nimitvijayvargee/zenithkb/pcb/zenithkb/led.kicad_sch

## KiCad design pcb/zenithkb/led.kicad_sch (2026-05-24)

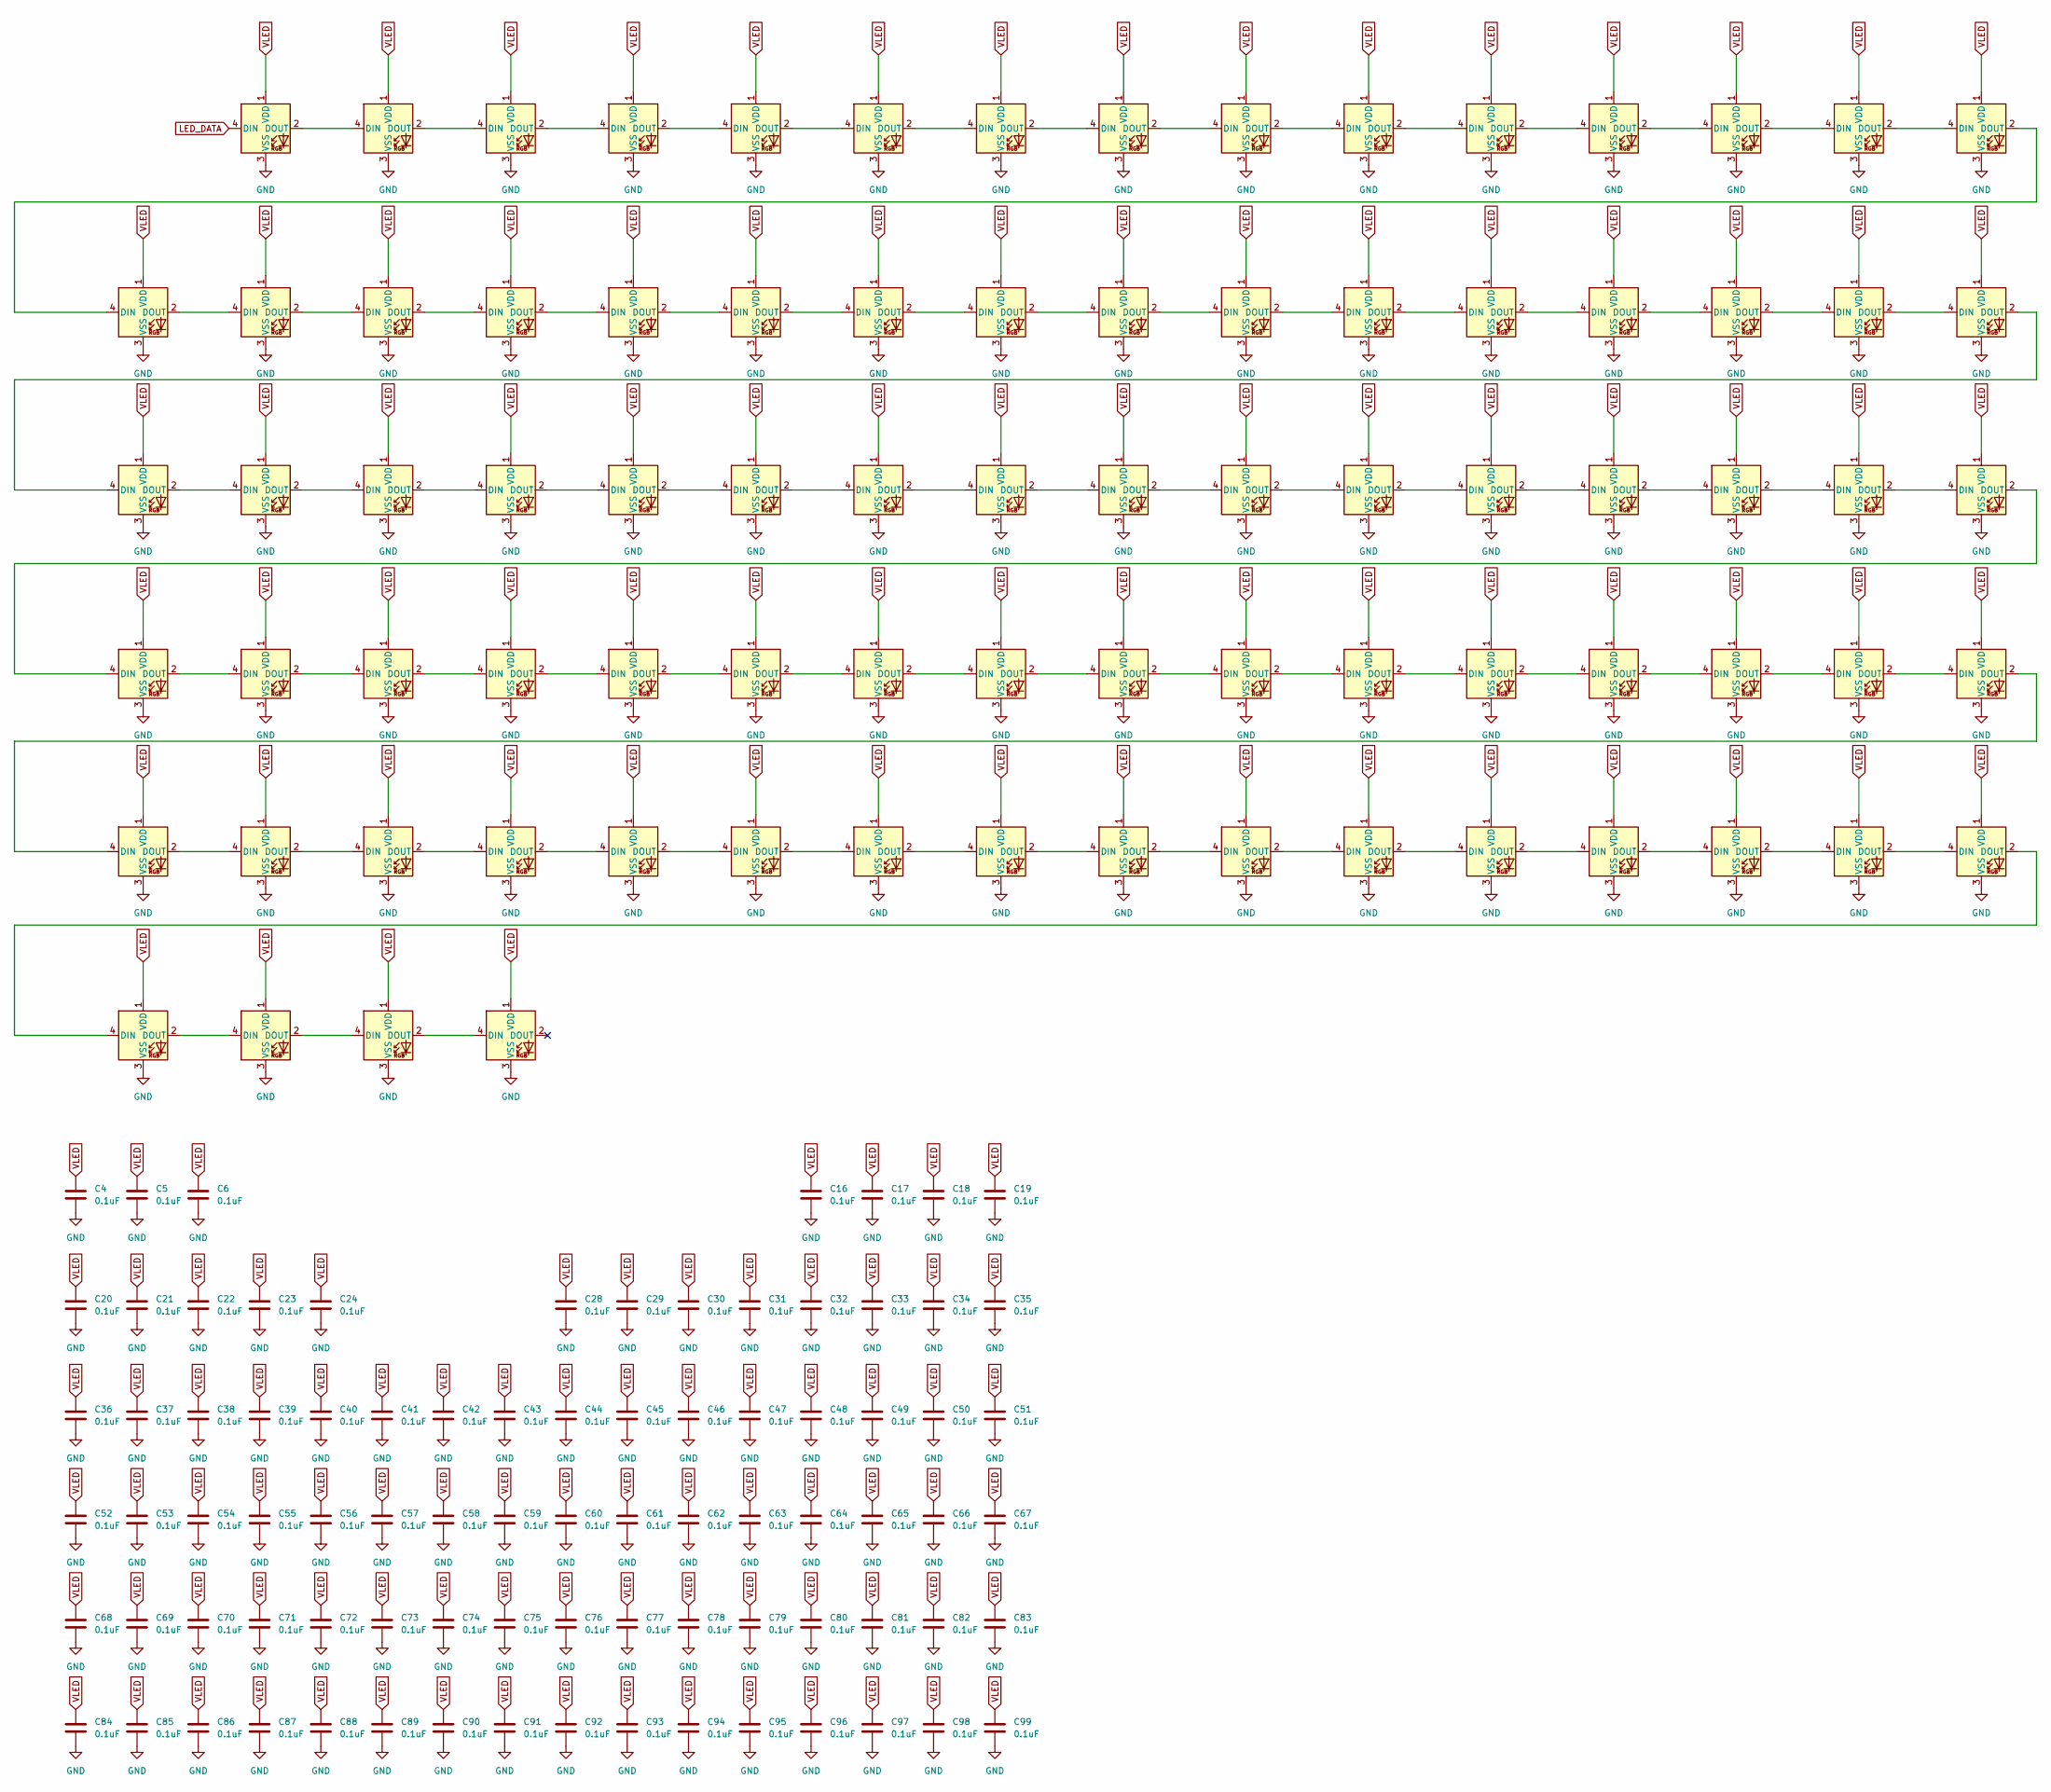
[picture p14: schematic led.kicad_sch]

Parts:
C4, C5, C6, C16, C17, C18, C19, C20, C21, C22, C23, C24, C28, C29, C30, C31, C32, C33, C34, C35, C36, C37, C38, C39, C40, C41, C42, C43, C44, C45, C46, C47, C48, C49, C50, C51, C52, C53, C54, C55, C56, C57, C58, C59, C60, C61, C62, C63, C64, C65, C66, C67, C68, C69, C70, C71, C72, C73, C74, C75, C76, C77, C78, C79, C80, C81, C82, C83, C84, C85, C86, C87, C88, C89, C90, C91, C92, C93, C94, C95, C96, C97, C98, C99: 0.1uF; C_Disc_D5.0mm_W2.5mm_P2.50mm
D86, D87, D88, D89, D90, D91, D92, D93, D94, D95, D96, D97, D98, D99, D100, D101, D102, D103, D104, D105, D106, D107, D108, D109, D110, D111, D112, D113, D114, D115, D116, D117, D118, D119, D120, D121, D122, D123, D124, D125, D126, D127, D128, D129, D130, D131, D132, D133, D134, D135, D136, D137, D138, D139, D140, D141, D142, D143, D144, D145, D146, D147, D148, D149, D150, D151, D152, D153, D154, D155, D156, D157, D158, D159, D160, D161, D162, D163, D164, D165, D166, D167, D168: LED_SK6812MINI; LCSC C5149201

Connections:
GND: C4.2, C5.2, C6.2, C16.2, C17.2, C18.2, C19.2, C20.2, C21.2, C22.2, C23.2, C24.2, C28.2, C29.2, C30.2, C31.2, C32.2, C33.2, C34.2, C35.2, C36.2, C37.2, C38.2, C39.2, C40.2, C41.2, C42.2, C43.2, C44.2, C45.2, C46.2, C47.2, C48.2, C49.2, C50.2, C51.2, C52.2, C53.2, C54.2, C55.2, C56.2, C57.2, C58.2, C59.2, C60.2, C61.2, C62.2, C63.2, C64.2, C65.2, C66.2, C67.2, C68.2, C69.2, C70.2, C71.2, C72.2, C73.2, C74.2, C75.2, C76.2, C77.2, C78.2, C79.2, C80.2, C81.2, C82.2, C83.2, C84.2, C85.2, C86.2, C87.2, C88.2, C89.2, C90.2, C91.2, C92.2, C93.2, C94.2, C95.2, C96.2, C97.2, C98.2, C99.2, D86.3 (VSS), D87.3 (VSS), D88.3 (VSS), D89.3 (VSS), D90.3 (VSS), D91.3 (VSS), D92.3 (VSS), D93.3 (VSS), D94.3 (VSS), D95.3 (VSS), D96.3 (VSS), D97.3 (VSS), D98.3 (VSS), D99.3 (VSS), D100.3 (VSS), D101.3 (VSS), D102.3 (VSS), D103.3 (VSS), D104.3 (VSS), D105.3 (VSS), D106.3 (VSS), D107.3 (VSS), D108.3 (VSS), D109.3 (VSS), D110.3 (VSS), D111.3 (VSS), D112.3 (VSS), D113.3 (VSS), D114.3 (VSS), D115.3 (VSS), D116.3 (VSS), D117.3 (VSS), D118.3 (VSS), D119.3 (VSS), D120.3 (VSS), D121.3 (VSS), D122.3 (VSS), D123.3 (VSS), D124.3 (VSS), D125.3 (VSS), D126.3 (VSS), D127.3 (VSS), D128.3 (VSS), D129.3 (VSS), D130.3 (VSS), D131.3 (VSS), D132.3 (VSS), D133.3 (VSS), D134.3 (VSS), D135.3 (VSS), D136.3 (VSS), D137.3 (VSS), D138.3 (VSS), D139.3 (VSS), D140.3 (VSS), D141.3 (VSS), D142.3 (VSS), D143.3 (VSS), D144.3 (VSS), D145.3 (VSS), D146.3 (VSS), D147.3 (VSS), D148.3 (VSS), D149.3 (VSS), D150.3 (VSS), D151.3 (VSS), D152.3 (VSS), D153.3 (VSS), D154.3 (VSS), D155.3 (VSS), D156.3 (VSS), D157.3 (VSS), D158.3 (VSS), D159.3 (VSS), D160.3 (VSS), D161.3 (VSS), D162.3 (VSS), D163.3 (VSS), D164.3 (VSS), D165.3 (VSS), D166.3 (VSS), D167.3 (VSS), D168.3 (VSS)
LED_DATA: D86.4 (DIN)
unnamed: D86.2 (DOUT), D87.4 (DIN)
unnamed: D87.2 (DOUT), D88.4 (DIN)
unnamed: D88.2 (DOUT), D89.4 (DIN)
unnamed: D89.2 (DOUT), D90.4 (DIN)
unnamed: D90.2 (DOUT), D91.4 (DIN)
unnamed: D91.2 (DOUT), D92.4 (DIN)
unnamed: D92.2 (DOUT), D93.4 (DIN)
unnamed: D93.2 (DOUT), D94.4 (DIN)
unnamed: D94.2 (DOUT), D95.4 (DIN)
unnamed: D95.2 (DOUT), D96.4 (DIN)
unnamed: D96.2 (DOUT), D97.4 (DIN)
unnamed: D97.2 (DOUT), D98.4 (DIN)
unnamed: D98.2 (DOUT), D99.4 (DIN)
unnamed: D100.2 (DOUT), D101.4 (DIN)
unnamed: D99.2 (DOUT), D100.4 (DIN)
unnamed: D101.2 (DOUT), D102.4 (DIN)
unnamed: D102.2 (DOUT), D103.4 (DIN)
unnamed: D103.2 (DOUT), D104.4 (DIN)
unnamed: D104.2 (DOUT), D105.4 (DIN)
unnamed: D105.2 (DOUT), D106.4 (DIN)
unnamed: D106.2 (DOUT), D107.4 (DIN)
unnamed: D107.2 (DOUT), D108.4 (DIN)
unnamed: D108.2 (DOUT), D109.4 (DIN)
unnamed: D109.2 (DOUT), D110.4 (DIN)
unnamed: D110.2 (DOUT), D111.4 (DIN)
unnamed: D111.2 (DOUT), D112.4 (DIN)
unnamed: D112.2 (DOUT), D113.4 (DIN)
unnamed: D113.2 (DOUT), D114.4 (DIN)
unnamed: D114.2 (DOUT), D115.4 (DIN)
unnamed: D115.2 (DOUT), D116.4 (DIN)
unnamed: D116.2 (DOUT), D117.4 (DIN)
unnamed: D117.2 (DOUT), D118.4 (DIN)
unnamed: D118.2 (DOUT), D119.4 (DIN)
unnamed: D119.2 (DOUT), D120.4 (DIN)
unnamed: D120.2 (DOUT), D121.4 (DIN)
unnamed: D121.2 (DOUT), D122.4 (DIN)
unnamed: D122.2 (DOUT), D123.4 (DIN)
unnamed: D123.2 (DOUT), D124.4 (DIN)
unnamed: D124.2 (DOUT), D125.4 (DIN)
unnamed: D125.2 (DOUT), D126.4 (DIN)
unnamed: D126.2 (DOUT), D127.4 (DIN)
unnamed: D127.2 (DOUT), D128.4 (DIN)
unnamed: D128.2 (DOUT), D129.4 (DIN)
unnamed: D129.2 (DOUT), D130.4 (DIN)
unnamed: D130.2 (DOUT), D131.4 (DIN)
unnamed: D131.2 (DOUT), D132.4 (DIN)
unnamed: D132.2 (DOUT), D133.4 (DIN)
unnamed: D133.2 (DOUT), D134.4 (DIN)
unnamed: D134.2 (DOUT), D135.4 (DIN)
unnamed: D135.2 (DOUT), D136.4 (DIN)
unnamed: D136.2 (DOUT), D137.4 (DIN)
unnamed: D137.2 (DOUT), D138.4 (DIN)
unnamed: D138.2 (DOUT), D139.4 (DIN)
unnamed: D139.2 (DOUT), D140.4 (DIN)
unnamed: D140.2 (DOUT), D141.4 (DIN)
unnamed: D141.2 (DOUT), D142.4 (DIN)
unnamed: D142.2 (DOUT), D143.4 (DIN)
unnamed: D143.2 (DOUT), D144.4 (DIN)
unnamed: D144.2 (DOUT), D145.4 (DIN)
unnamed: D145.2 (DOUT), D146.4 (DIN)
unnamed: D146.2 (DOUT), D147.4 (DIN)
unnamed: D147.2 (DOUT), D148.4 (DIN)
unnamed: D148.2 (DOUT), D149.4 (DIN)
unnamed: D149.2 (DOUT), D150.4 (DIN)
unnamed: D150.2 (DOUT), D151.4 (DIN)
unnamed: D151.2 (DOUT), D152.4 (DIN)
unnamed: D152.2 (DOUT), D153.4 (DIN)
unnamed: D153.2 (DOUT), D154.4 (DIN)
unnamed: D154.2 (DOUT), D155.4 (DIN)
unnamed: D155.2 (DOUT), D156.4 (DIN)
unnamed: D156.2 (DOUT), D157.4 (DIN)
unnamed: D157.2 (DOUT), D158.4 (DIN)
unnamed: D158.2 (DOUT), D159.4 (DIN)
unnamed: D159.2 (DOUT), D160.4 (DIN)
unnamed: D160.2 (DOUT), D161.4 (DIN)
unnamed: D161.2 (DOUT), D162.4 (DIN)
unnamed: D162.2 (DOUT), D163.4 (DIN)
unnamed: D163.2 (DOUT), D164.4 (DIN)
unnamed: D164.2 (DOUT), D165.4 (DIN)
unnamed: D165.2 (DOUT), D166.4 (DIN)
unnamed: D166.2 (DOUT), D167.4 (DIN)
unnamed: D167.2 (DOUT), D168.4 (DIN)
VLED: C4.1, C5.1, C6.1, C16.1, C17.1, C18.1, C19.1, C20.1, C21.1, C22.1, C23.1, C24.1, C28.1, C29.1, C30.1, C31.1, C32.1, C33.1, C34.1, C35.1, C36.1, C37.1, C38.1, C39.1, C40.1, C41.1, C42.1, C43.1, C44.1, C45.1, C46.1, C47.1, C48.1, C49.1, C50.1, C51.1, C52.1, C53.1, C54.1, C55.1, C56.1, C57.1, C58.1, C59.1, C60.1, C61.1, C62.1, C63.1, C64.1, C65.1, C66.1, C67.1, C68.1, C69.1, C70.1, C71.1, C72.1, C73.1, C74.1, C75.1, C76.1, C77.1, C78.1, C79.1, C80.1, C81.1, C82.1, C83.1, C84.1, C85.1, C86.1, C87.1, C88.1, C89.1, C90.1, C91.1, C92.1, C93.1, C94.1, C95.1, C96.1, C97.1, C98.1, C99.1, D86.1 (VDD), D87.1 (VDD), D88.1 (VDD), D89.1 (VDD), D90.1 (VDD), D91.1 (VDD), D92.1 (VDD), D93.1 (VDD), D94.1 (VDD), D95.1 (VDD), D96.1 (VDD), D97.1 (VDD), D98.1 (VDD), D99.1 (VDD), D100.1 (VDD), D101.1 (VDD), D102.1 (VDD), D103.1 (VDD), D104.1 (VDD), D105.1 (VDD), D106.1 (VDD), D107.1 (VDD), D108.1 (VDD), D109.1 (VDD), D110.1 (VDD), D111.1 (VDD), D112.1 (VDD), D113.1 (VDD), D114.1 (VDD), D115.1 (VDD), D116.1 (VDD), D117.1 (VDD), D118.1 (VDD), D119.1 (VDD), D120.1 (VDD), D121.1 (VDD), D122.1 (VDD), D123.1 (VDD), D124.1 (VDD), D125.1 (VDD), D126.1 (VDD), D127.1 (VDD), D128.1 (VDD), D129.1 (VDD), D130.1 (VDD), D131.1 (VDD), D132.1 (VDD), D133.1 (VDD), D134.1 (VDD), D135.1 (VDD), D136.1 (VDD), D137.1 (VDD), D138.1 (VDD), D139.1 (VDD), D140.1 (VDD), D141.1 (VDD), D142.1 (VDD), D143.1 (VDD), D144.1 (VDD), D145.1 (VDD), D146.1 (VDD), D147.1 (VDD), D148.1 (VDD), D149.1 (VDD), D150.1 (VDD), D151.1 (VDD), D152.1 (VDD), D153.1 (VDD), D154.1 (VDD), D155.1 (VDD), D156.1 (VDD), D157.1 (VDD), D158.1 (VDD), D159.1 (VDD), D160.1 (VDD), D161.1 (VDD), D162.1 (VDD), D163.1 (VDD), D164.1 (VDD), D165.1 (VDD), D166.1 (VDD), D167.1 (VDD), D168.1 (VDD)
