nimitvijayvargee/zenithkb/pcb/zenithkb/macropad.kicad_sch

## KiCad design pcb/zenithkb/macropad.kicad_sch (2026-05-24)

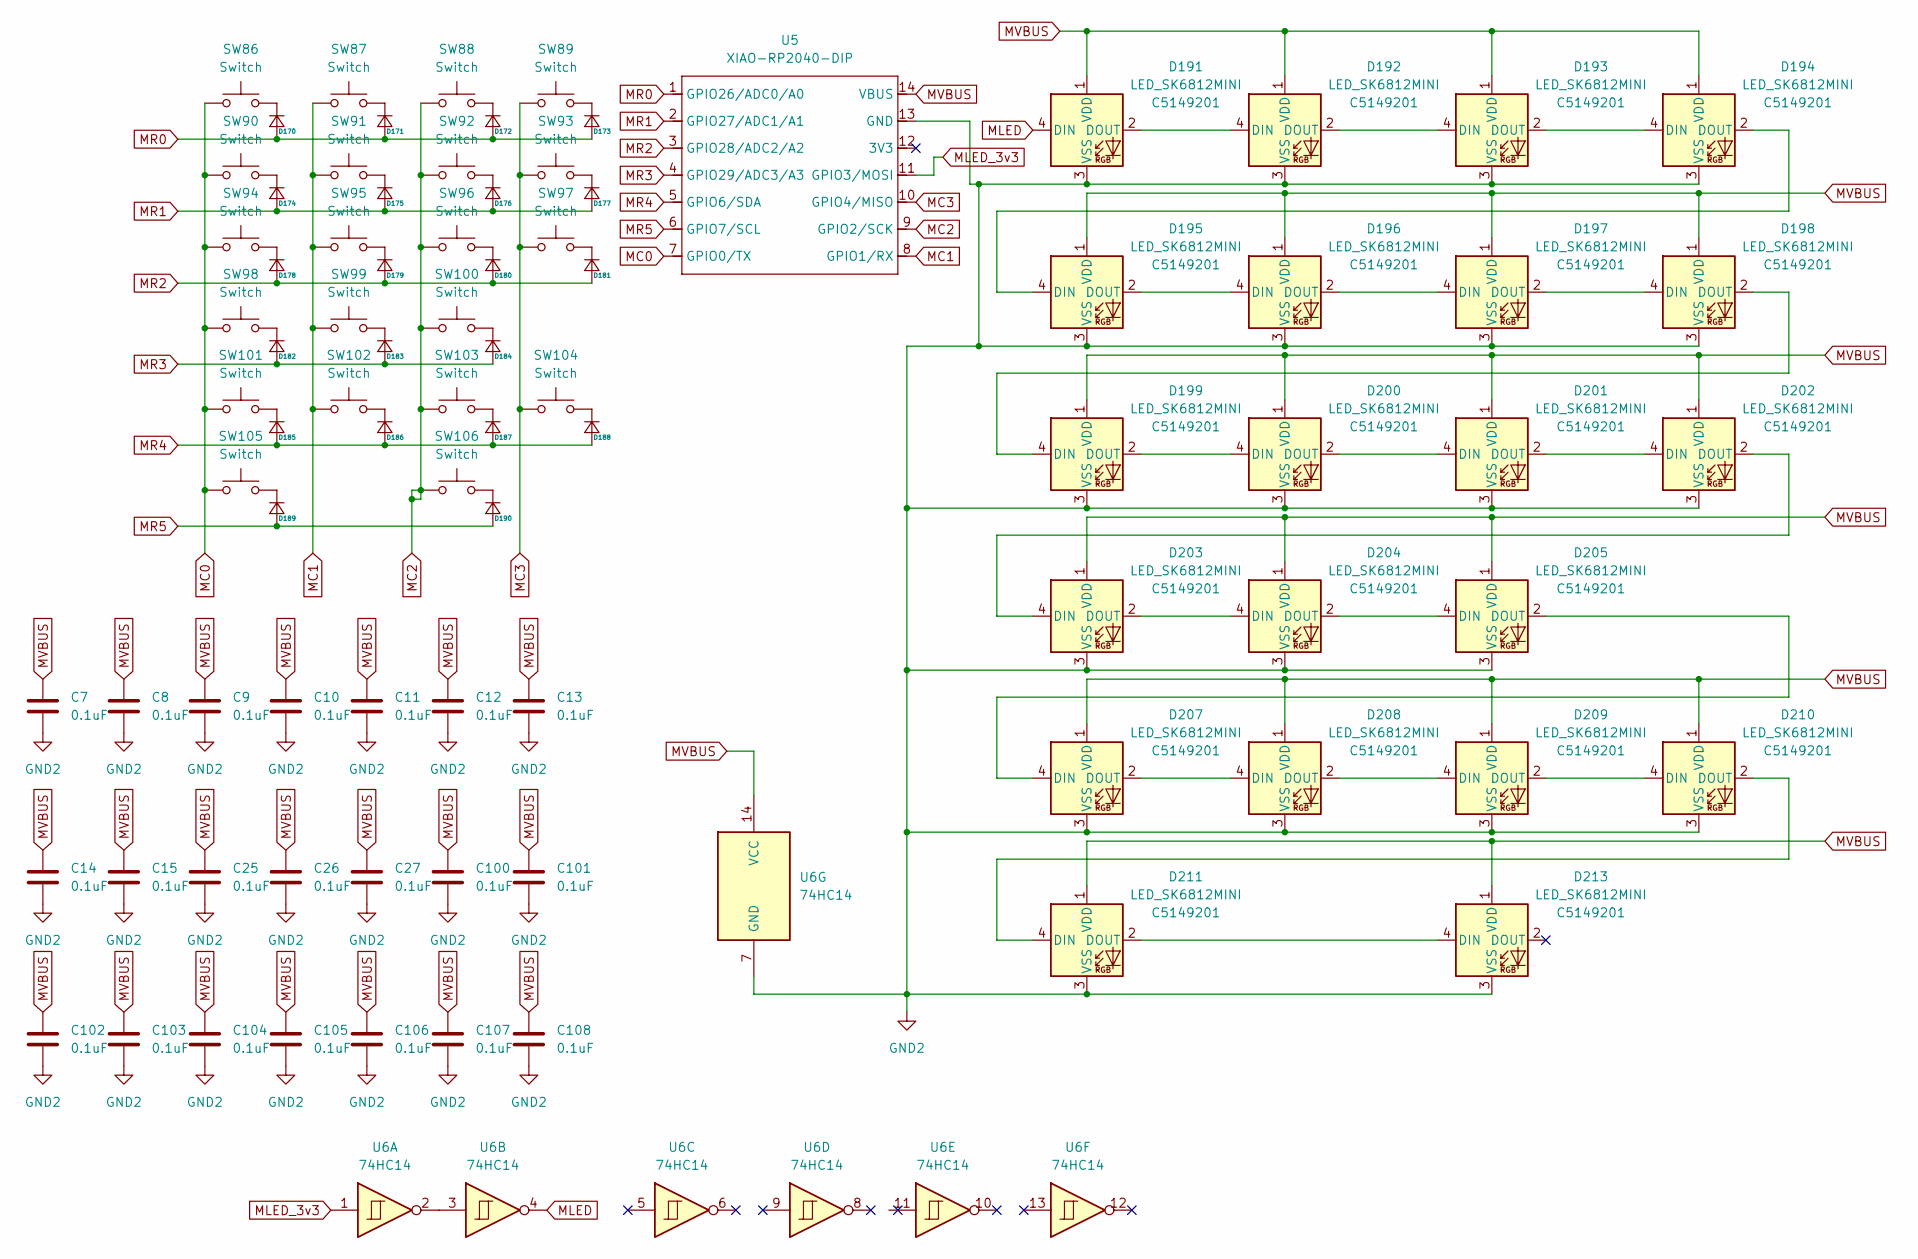
[picture p15: schematic macropad.kicad_sch]

Parts:
C7, C8, C9, C10, C11, C12, C13, C14, C15, C25, C26, C27, C100, C101, C102, C103, C104, C105, C106, C107, C108: 0.1uF; C_Disc_D5.0mm_W2.5mm_P2.50mm
D170, D171, D172, D173, D174, D175, D176, D177, D178, D179, D180, D181, D182, D183, D184, D185, D186, D187, D188, D189, D190: D_DO-35_SOD27_P7.62mm_Horizontal
D191, D192, D193, D194, D195, D196, D197, D198, D199, D200, D201, D202, D203, D204, D205, D207, D208, D209, D210, D211, D213: LED_SK6812MINI; LCSC C5149201
SW86, SW87, SW88, SW89, SW90, SW91, SW92, SW93, SW94, SW95, SW96, SW98, SW99, SW100, SW101, SW102, SW103, SW106: Switch; Hotswap_MX_1.00u
SW97, SW104: Switch; Hotswap_MX_2.00u_90deg
SW105: Switch; Hotswap_MX_2.00u
U5: XIAO-RP2040-DIP
U6: 74HC14; DIP-14_W7.62mm

Connections:
GND2: C7.2, C8.2, C9.2, C10.2, C11.2, C12.2, C13.2, C14.2, C15.2, C25.2, C26.2, C27.2, C100.2, C101.2, C102.2, C103.2, C104.2, C105.2, C106.2, C107.2, C108.2, D191.3 (VSS), D192.3 (VSS), D193.3 (VSS), D194.3 (VSS), D195.3 (VSS), D196.3 (VSS), D197.3 (VSS), D198.3 (VSS), D199.3 (VSS), D200.3 (VSS), D201.3 (VSS), D202.3 (VSS), D203.3 (VSS), D204.3 (VSS), D205.3 (VSS), D207.3 (VSS), D208.3 (VSS), D209.3 (VSS), D210.3 (VSS), D211.3 (VSS), D213.3 (VSS), U5.13 (GND), U6.7 (GND)
MC0: SW86.1, SW90.1, SW94.1, SW98.1, SW101.1, SW105.1, U5.7 (GPIO0/TX)
MC1: SW87.1, SW91.1, SW95.1, SW99.1, SW102.1, U5.8 (GPIO1/RX)
MC2: SW88.1, SW92.1, SW96.1, SW100.1, SW103.1, SW106.1, U5.9 (GPIO2/SCK)
MC3: SW89.1, SW93.1, SW97.1, SW104.1, U5.10 (GPIO4/MISO)
MLED: D191.4 (DIN), U6.4
MLED_3v3: U5.11 (GPIO3/MOSI), U6.1
MR0: D170.2 (A), D171.2 (A), D172.2 (A), D173.2 (A), U5.1 (GPIO26/ADC0/A0)
MR1: D174.2 (A), D175.2 (A), D176.2 (A), D177.2 (A), U5.2 (GPIO27/ADC1/A1)
MR2: D178.2 (A), D179.2 (A), D180.2 (A), D181.2 (A), U5.3 (GPIO28/ADC2/A2)
MR3: D182.2 (A), D183.2 (A), D184.2 (A), U5.4 (GPIO29/ADC3/A3)
MR4: D185.2 (A), D186.2 (A), D187.2 (A), D188.2 (A), U5.5 (GPIO6/SDA)
MR5: D189.2 (A), D190.2 (A), U5.6 (GPIO7/SCL)
MVBUS: C7.1, C8.1, C9.1, C10.1, C11.1, C12.1, C13.1, C14.1, C15.1, C25.1, C26.1, C27.1, C100.1, C101.1, C102.1, C103.1, C104.1, C105.1, C106.1, C107.1, C108.1, D191.1 (VDD), D192.1 (VDD), D193.1 (VDD), D194.1 (VDD), D195.1 (VDD), D196.1 (VDD), D197.1 (VDD), D198.1 (VDD), D199.1 (VDD), D200.1 (VDD), D201.1 (VDD), D202.1 (VDD), D203.1 (VDD), D204.1 (VDD), D205.1 (VDD), D207.1 (VDD), D208.1 (VDD), D209.1 (VDD), D210.1 (VDD), D211.1 (VDD), D213.1 (VDD), U5.14 (VBUS), U6.14 (VCC)
unnamed: D170.1 (K), SW86.2
unnamed: D171.1 (K), SW87.2
unnamed: D172.1 (K), SW88.2
unnamed: D173.1 (K), SW89.2
unnamed: D174.1 (K), SW90.2
unnamed: D175.1 (K), SW91.2
unnamed: D176.1 (K), SW92.2
unnamed: D177.1 (K), SW93.2
unnamed: D178.1 (K), SW94.2
unnamed: D179.1 (K), SW95.2
unnamed: D180.1 (K), SW96.2
unnamed: D181.1 (K), SW97.2
unnamed: D182.1 (K), SW98.2
unnamed: D183.1 (K), SW99.2
unnamed: D184.1 (K), SW100.2
unnamed: D185.1 (K), SW101.2
unnamed: D186.1 (K), SW102.2
unnamed: D187.1 (K), SW103.2
unnamed: D188.1 (K), SW104.2
unnamed: D189.1 (K), SW105.2
unnamed: D190.1 (K), SW106.2
unnamed: D191.2 (DOUT), D192.4 (DIN)
unnamed: D192.2 (DOUT), D193.4 (DIN)
unnamed: D193.2 (DOUT), D194.4 (DIN)
unnamed: D194.2 (DOUT), D195.4 (DIN)
unnamed: D195.2 (DOUT), D196.4 (DIN)
unnamed: D196.2 (DOUT), D197.4 (DIN)
unnamed: D197.2 (DOUT), D198.4 (DIN)
unnamed: D198.2 (DOUT), D199.4 (DIN)
unnamed: D199.2 (DOUT), D200.4 (DIN)
unnamed: D200.2 (DOUT), D201.4 (DIN)
unnamed: D201.2 (DOUT), D202.4 (DIN)
unnamed: D202.2 (DOUT), D203.4 (DIN)
unnamed: D203.2 (DOUT), D204.4 (DIN)
unnamed: D204.2 (DOUT), D205.4 (DIN)
unnamed: D205.2 (DOUT), D207.4 (DIN)
unnamed: D207.2 (DOUT), D208.4 (DIN)
unnamed: D208.2 (DOUT), D209.4 (DIN)
unnamed: D209.2 (DOUT), D210.4 (DIN)
unnamed: D210.2 (DOUT), D211.4 (DIN)
unnamed: D211.2 (DOUT), D213.4 (DIN)
unnamed: U6.2, U6.3
