nimitvijayvargee/zenithkb/pcb/zenithkb/zenithkb.kicad_sch

## KiCad design pcb/zenithkb/zenithkb.kicad_sch (2026-05-24)

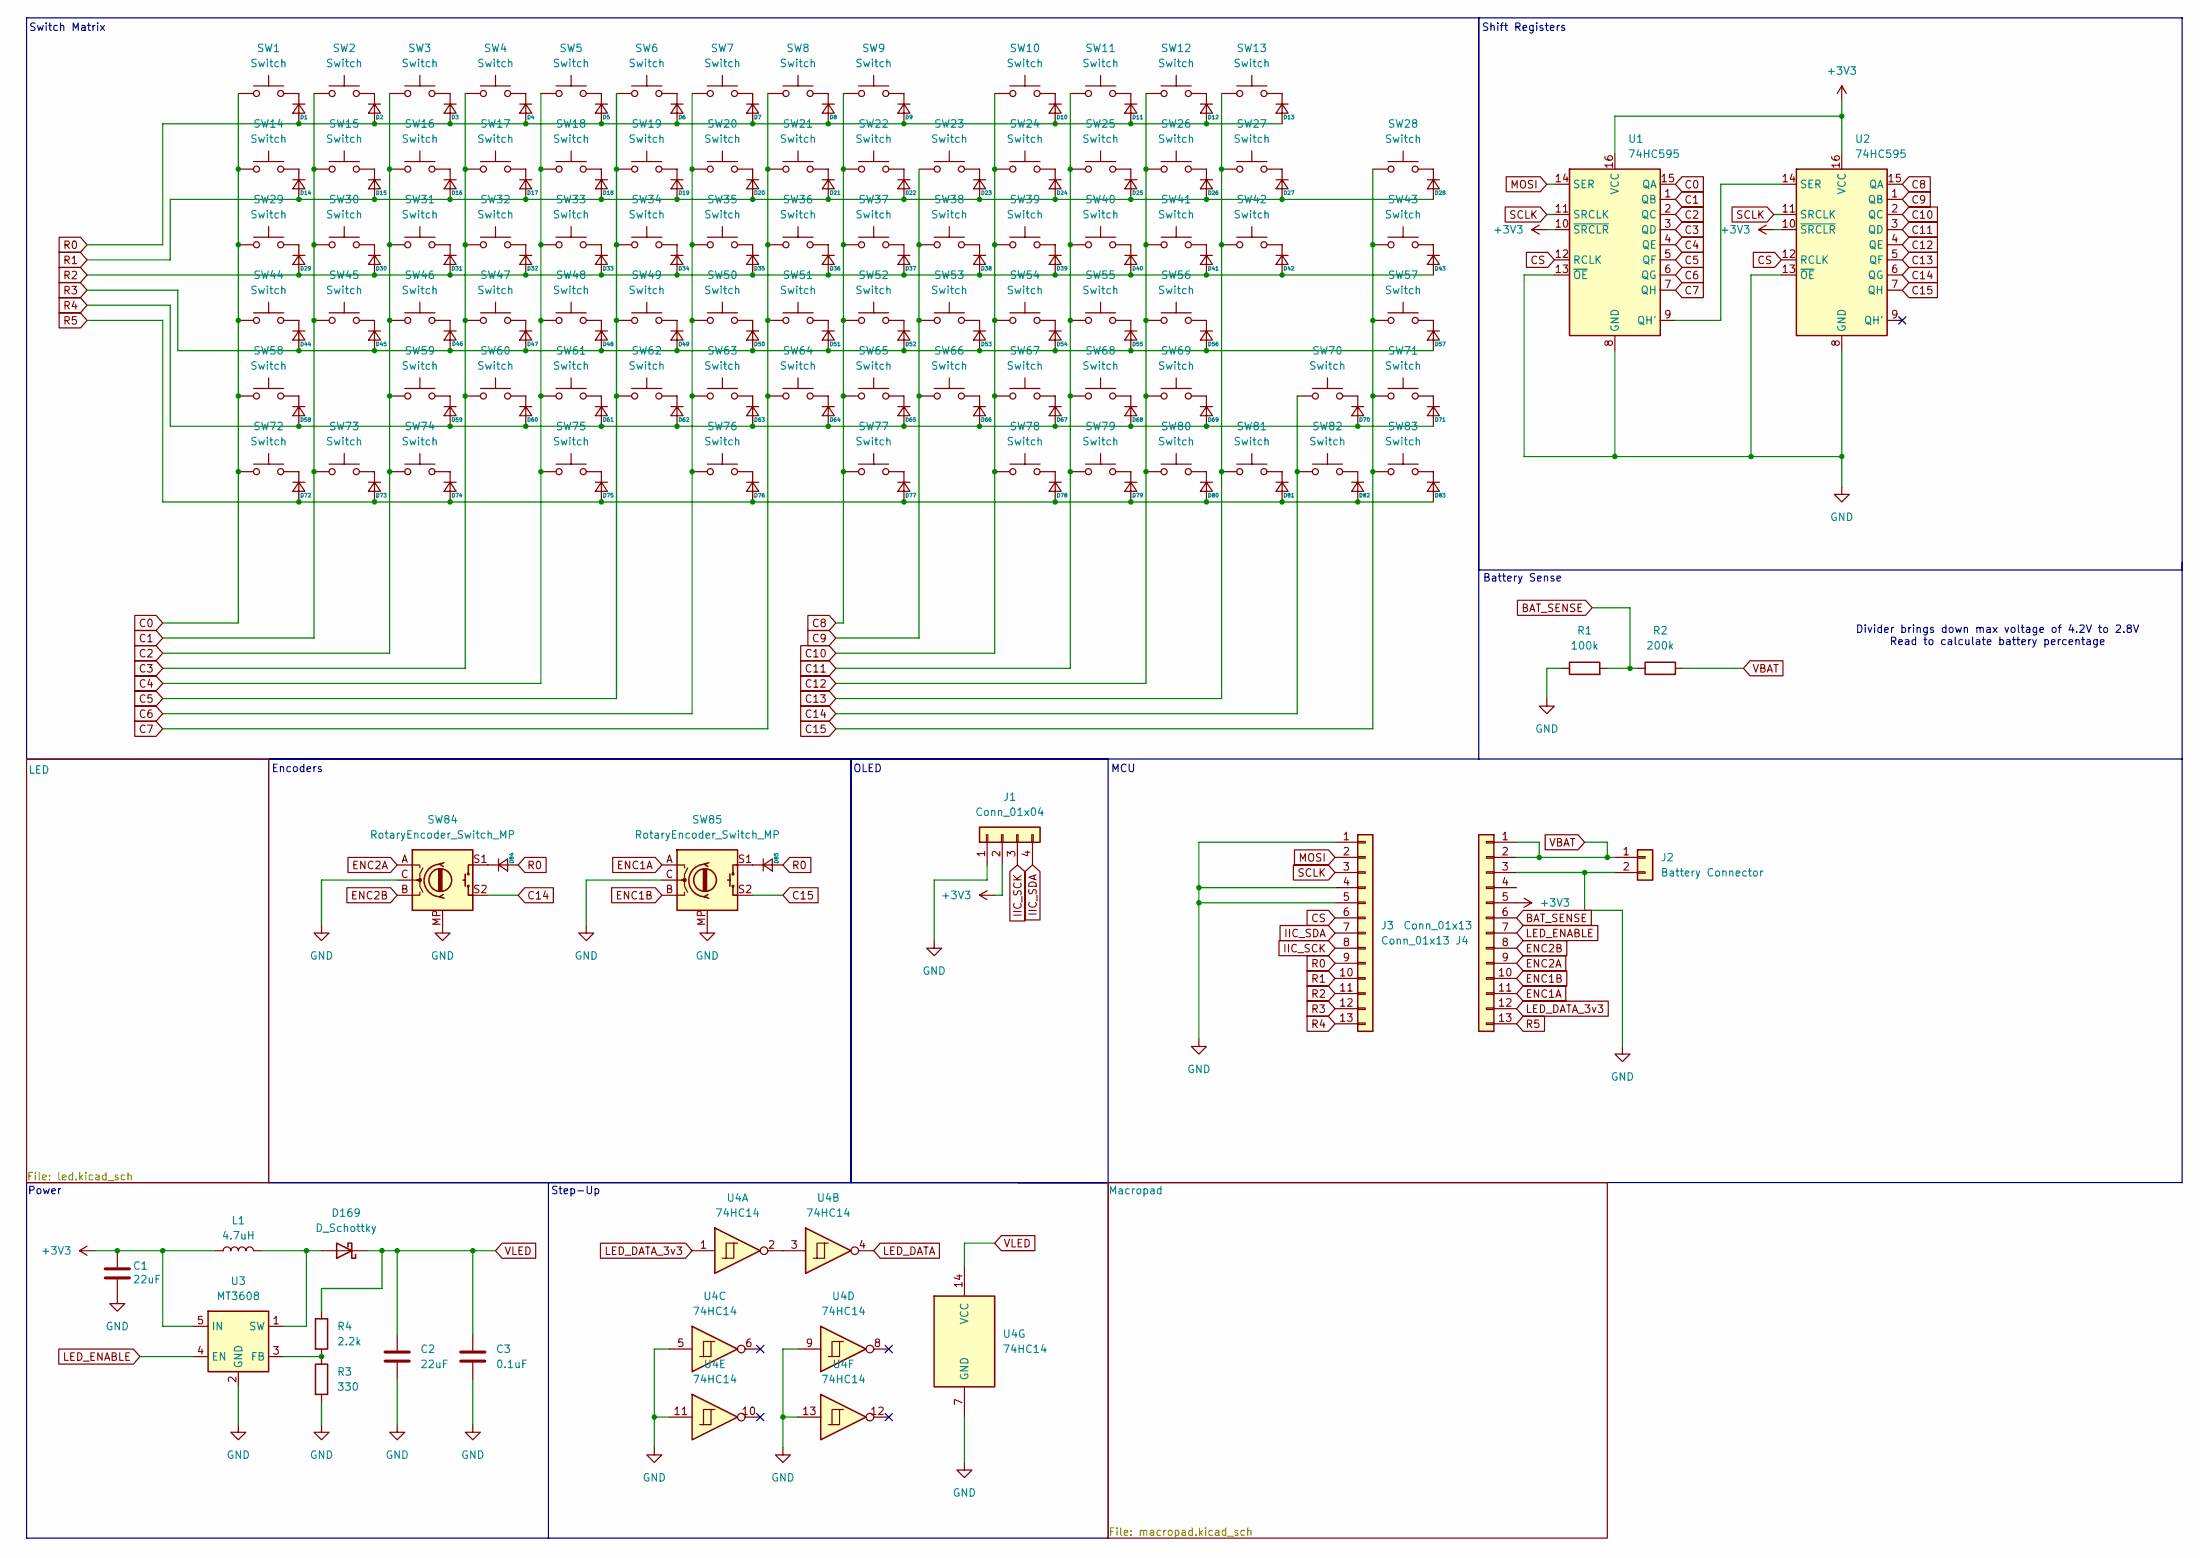
[picture p16: schematic zenithkb.kicad_sch]

Parts:
C1, C2: 22uF; C_Disc_D5.0mm_W2.5mm_P2.50mm
C3: 0.1uF; C_Disc_D5.0mm_W2.5mm_P2.50mm
D1, D2, D3, D4, D5, D6, D7, D8, D9, D10, D11, D12, D13, D14, D15, D16, D17, D18, D19, D20, D21, D22, D23, D24, D25, D26, D27, D28, D29, D30, D31, D32, D33, D34, D35, D36, D37, D38, D39, D40, D41, D42, D43, D44, D45, D46, D47, D48, D49, D50, D51, D52, D53, D54, D55, D56, D57, D58, D59, D60, D61, D62, D63, D64, D65, D66, D67, D68, D69, D70, D71, D72, D73, D74, D75, D76, D77, D78, D79, D80, D81, D82, D83, D84, D85: D_DO-35_SOD27_P7.62mm_Horizontal
D169: D_Schottky; D_SMA_Handsoldering
J1: Conn_01x04; PinSocket_1x04_P2.54mm_Vertical
J2: Battery Connector; PinSocket_1x02_P2.54mm_Vertical
J3, J4: Conn_01x13; PinHeader_1x13_P2.54mm_Vertical
L1: 4.7uH; L_Sunlord_SWPA5040S
R1: 100k; R_Axial_DIN0207_L6.3mm_D2.5mm_P7.62mm_Horizontal
R2: 200k; R_Axial_DIN0207_L6.3mm_D2.5mm_P7.62mm_Horizontal
R3: 330; R_Axial_DIN0207_L6.3mm_D2.5mm_P7.62mm_Horizontal
R4: 2.2k; R_Axial_DIN0207_L6.3mm_D2.5mm_P7.62mm_Horizontal
SW1, SW2, SW3, SW4, SW5, SW6, SW7, SW8, SW9, SW10, SW11, SW12, SW13, SW14, SW15, SW16, SW17, SW18, SW19, SW20, SW21, SW22, SW23, SW24, SW25, SW26, SW28, SW30, SW31, SW32, SW33, SW34, SW35, SW36, SW37, SW38, SW39, SW40, SW41, SW43, SW45, SW46, SW47, SW48, SW49, SW50, SW51, SW52, SW53, SW54, SW55, SW57, SW59, SW60, SW61, SW62, SW63, SW64, SW65, SW66, SW67, SW68, SW70, SW71, SW78, SW79, SW80, SW81, SW82, SW83: Switch; Hotswap_MX_1.00u
SW27, SW75, SW77: Switch; Hotswap_MX_2.00u
SW29, SW42: Switch; Hotswap_MX_1.50u
SW44, SW69: Switch; Hotswap_MX_1.75u
SW56, SW58, SW76: Switch; Hotswap_MX_2.25u
SW72, SW73, SW74: Switch; Hotswap_MX_1.25u
SW84, SW85: RotaryEncoder_Switch_MP; RotaryEncoder_Alps_EC11E-Switch_Vertical_H20mm_MountingHoles
U1, U2: 74HC595; DIP-16_W7.62mm
U3: MT3608; SOT-23-6_Handsoldering
U4: 74HC14; DIP-14_W7.62mm

Connections:
+3V3: C1.1, J1.2, J4.5, L1.1, U1.10 (~SRCLR), U1.16 (VCC), U2.10 (~SRCLR), U2.16 (VCC), U3.5 (IN)
BAT_SENSE: J4.6, R1.2, R2.1
C0: SW1.1, SW14.1, SW29.1, SW44.1, SW58.1, SW72.1, U1.15 (QA)
C1: SW2.1, SW15.1, SW30.1, SW45.1, SW73.1, U1.1 (QB)
C2: SW3.1, SW16.1, SW31.1, SW46.1, SW59.1, SW74.1, U1.2 (QC)
C3: SW4.1, SW17.1, SW32.1, SW47.1, SW60.1, U1.3 (QD)
C4: SW5.1, SW18.1, SW33.1, SW48.1, SW61.1, SW75.1, U1.4 (QE)
C5: SW6.1, SW19.1, SW34.1, SW49.1, SW62.1, U1.5 (QF)
C6: SW7.1, SW20.1, SW35.1, SW50.1, SW63.1, SW76.1, U1.6 (QG)
C7: SW8.1, SW21.1, SW36.1, SW51.1, SW64.1, U1.7 (QH)
C8: SW9.1, SW22.1, SW37.1, SW52.1, SW65.1, SW77.1, U2.15 (QA)
C9: SW23.1, SW38.1, SW53.1, SW66.1, U2.1 (QB)
C10: SW10.1, SW24.1, SW39.1, SW54.1, SW67.1, SW78.1, U2.2 (QC)
C11: SW11.1, SW25.1, SW40.1, SW55.1, SW68.1, SW79.1, U2.3 (QD)
C12: SW12.1, SW26.1, SW41.1, SW56.1, SW69.1, SW80.1, U2.4 (QE)
C13: SW13.1, SW27.1, SW42.1, SW81.1, U2.5 (QF)
C14: SW70.1, SW82.1, SW84.S2, U2.6 (QG)
C15: SW28.1, SW43.1, SW57.1, SW71.1, SW83.1, SW85.S2, U2.7 (QH)
CS: J3.6, U1.12 (RCLK), U2.12 (RCLK)
ENC1A: J4.11, SW85.A
ENC1B: J4.10, SW85.B
ENC2A: J4.9, SW84.A
ENC2B: J4.8, SW84.B
GND: C1.2, C2.2, C3.2, J1.1, J2.2, J3.1, J3.4, J3.5, J4.3, R1.1, R3.2, SW84.C, SW84.MP, SW85.C, SW85.MP, U1.8 (GND), U1.13 (~OE), U2.8 (GND), U2.13 (~OE), U3.2 (GND), U4.5, U4.7 (GND), U4.9, U4.11, U4.13
IIC_SCK: J1.3, J3.8
IIC_SDA: J1.4, J3.7
LED_DATA: U4.4
LED_DATA_3v3: J4.12, U4.1
LED_ENABLE: J4.7, U3.4 (EN)
MOSI: J3.2, U1.14 (SER)
unnamed: D1.1 (K), SW1.2
unnamed: D2.1 (K), SW2.2
unnamed: D3.1 (K), SW3.2
unnamed: D4.1 (K), SW4.2
unnamed: D5.1 (K), SW5.2
unnamed: D6.1 (K), SW6.2
unnamed: D7.1 (K), SW7.2
unnamed: D8.1 (K), SW8.2
unnamed: D9.1 (K), SW9.2
unnamed: D10.1 (K), SW10.2
unnamed: D11.1 (K), SW11.2
unnamed: D12.1 (K), SW12.2
unnamed: D13.1 (K), SW13.2
unnamed: D14.1 (K), SW14.2
unnamed: D15.1 (K), SW15.2
unnamed: D16.1 (K), SW16.2
unnamed: D17.1 (K), SW17.2
unnamed: D18.1 (K), SW18.2
unnamed: D19.1 (K), SW19.2
unnamed: D20.1 (K), SW20.2
unnamed: D21.1 (K), SW21.2
unnamed: D22.1 (K), SW22.2
unnamed: D23.1 (K), SW23.2
unnamed: D24.1 (K), SW24.2
unnamed: D25.1 (K), SW25.2
unnamed: D26.1 (K), SW26.2
unnamed: D27.1 (K), SW27.2
unnamed: D28.1 (K), SW28.2
unnamed: D29.1 (K), SW29.2
unnamed: D30.1 (K), SW30.2
unnamed: D31.1 (K), SW31.2
unnamed: D32.1 (K), SW32.2
unnamed: D33.1 (K), SW33.2
unnamed: D34.1 (K), SW34.2
unnamed: D35.1 (K), SW35.2
unnamed: D36.1 (K), SW36.2
unnamed: D37.1 (K), SW37.2
unnamed: D38.1 (K), SW38.2
unnamed: D39.1 (K), SW39.2
unnamed: D40.1 (K), SW40.2
unnamed: D41.1 (K), SW41.2
unnamed: D42.1 (K), SW42.2
unnamed: D43.1 (K), SW43.2
unnamed: D44.1 (K), SW44.2
unnamed: D45.1 (K), SW45.2
unnamed: D46.1 (K), SW46.2
unnamed: D47.1 (K), SW47.2
unnamed: D48.1 (K), SW48.2
unnamed: D49.1 (K), SW49.2
unnamed: D50.1 (K), SW50.2
unnamed: D51.1 (K), SW51.2
unnamed: D52.1 (K), SW52.2
unnamed: D53.1 (K), SW53.2
unnamed: D54.1 (K), SW54.2
unnamed: D55.1 (K), SW55.2
unnamed: D56.1 (K), SW56.2
unnamed: D57.1 (K), SW57.2
unnamed: D58.1 (K), SW58.2
unnamed: D59.1 (K), SW59.2
unnamed: D60.1 (K), SW60.2
unnamed: D61.1 (K), SW61.2
unnamed: D62.1 (K), SW62.2
unnamed: D63.1 (K), SW63.2
unnamed: D64.1 (K), SW64.2
unnamed: D65.1 (K), SW65.2
unnamed: D66.1 (K), SW66.2
unnamed: D67.1 (K), SW67.2
unnamed: D68.1 (K), SW68.2
unnamed: D69.1 (K), SW69.2
unnamed: D70.1 (K), SW70.2
unnamed: D71.1 (K), SW71.2
unnamed: D72.1 (K), SW72.2
unnamed: D73.1 (K), SW73.2
unnamed: D74.1 (K), SW74.2
unnamed: D75.1 (K), SW75.2
unnamed: D76.1 (K), SW76.2
unnamed: D77.1 (K), SW77.2
unnamed: D78.1 (K), SW78.2
unnamed: D79.1 (K), SW79.2
unnamed: D80.1 (K), SW80.2
unnamed: D81.1 (K), SW81.2
unnamed: D82.1 (K), SW82.2
unnamed: D83.1 (K), SW83.2
unnamed: D84.1 (K), SW84.S1
unnamed: D85.1 (K), SW85.S1
unnamed: D169.2 (A), L1.2, U3.1 (SW)
unnamed: R3.1, R4.2, U3.3 (FB)
unnamed: U1.9 (QH'), U2.14 (SER)
unnamed: U4.2, U4.3
R0: D1.2 (A), D2.2 (A), D3.2 (A), D4.2 (A), D5.2 (A), D6.2 (A), D7.2 (A), D8.2 (A), D9.2 (A), D10.2 (A), D11.2 (A), D12.2 (A), D13.2 (A), D84.2 (A), D85.2 (A), J3.9
R1: D14.2 (A), D15.2 (A), D16.2 (A), D17.2 (A), D18.2 (A), D19.2 (A), D20.2 (A), D21.2 (A), D22.2 (A), D23.2 (A), D24.2 (A), D25.2 (A), D26.2 (A), D27.2 (A), D28.2 (A), J3.10
R2: D29.2 (A), D30.2 (A), D31.2 (A), D32.2 (A), D33.2 (A), D34.2 (A), D35.2 (A), D36.2 (A), D37.2 (A), D38.2 (A), D39.2 (A), D40.2 (A), D41.2 (A), D42.2 (A), D43.2 (A), J3.11
R3: D44.2 (A), D45.2 (A), D46.2 (A), D47.2 (A), D48.2 (A), D49.2 (A), D50.2 (A), D51.2 (A), D52.2 (A), D53.2 (A), D54.2 (A), D55.2 (A), D56.2 (A), D57.2 (A), J3.12
R4: D58.2 (A), D59.2 (A), D60.2 (A), D61.2 (A), D62.2 (A), D63.2 (A), D64.2 (A), D65.2 (A), D66.2 (A), D67.2 (A), D68.2 (A), D69.2 (A), D70.2 (A), D71.2 (A), J3.13
R5: D72.2 (A), D73.2 (A), D74.2 (A), D75.2 (A), D76.2 (A), D77.2 (A), D78.2 (A), D79.2 (A), D80.2 (A), D81.2 (A), D82.2 (A), D83.2 (A), J4.13
SCLK: J3.3, U1.11 (SRCLK), U2.11 (SRCLK)
VBAT: J2.1, J4.1, J4.2, R2.2
VLED: C2.1, C3.1, D169.1 (K), R4.1, U4.14 (VCC)

Notes on the sheet:
OLED
Battery Sense
Shift Registers
Switch Matrix
Power
Step-Up
MCU
Encoders
Divider brings down max voltage of 4.2V to 2.8V Read to calculate battery percentage
